mubarizahmed/desk_control/eda/desk_control_b.png

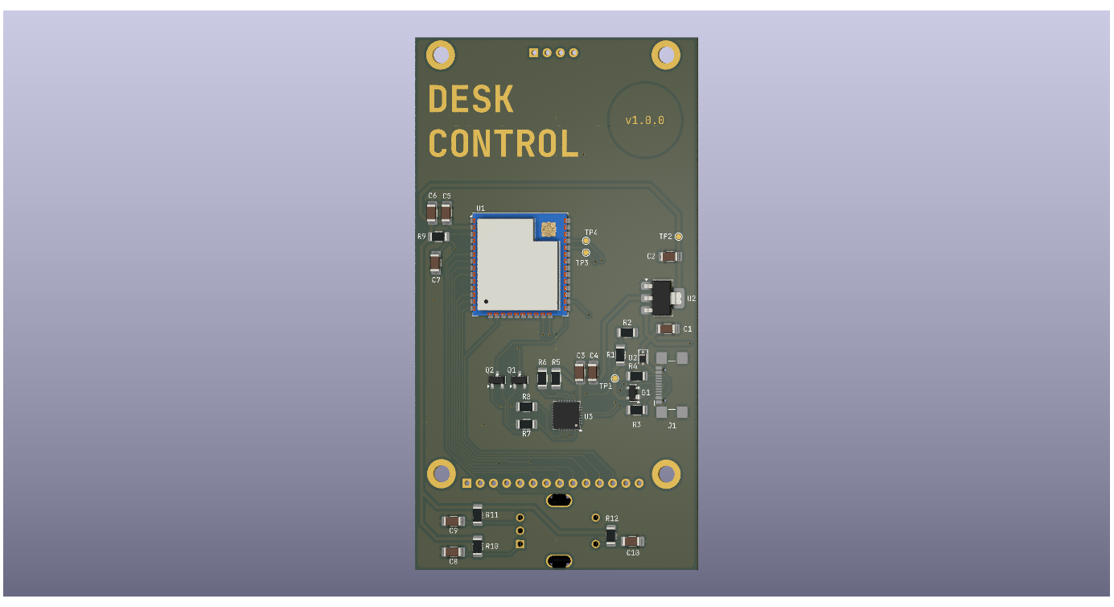
eda/desk_control_b.png
