mubarizahmed/desk_control/main/calendar_serv.h

/**
 * @file calendar_serv.h
 * @author Mubariz Ahmed (mubariz@mubariz.me)
 * @brief Header - Calendar service for fetching calendar data from a google script URL.
 * @version 0.1
 * @date 2025-04-13
 *
 */

#ifndef CALENDAR_SERV_H
#define CALENDAR_SERV_H

/* ------------------------------------------------------ */
/*                    PUBLIC FUNCTIONS                    */
/* ------------------------------------------------------ */

void calendar_task(void *pvParameters);

#endif // CALENDAR_SERV_H
