mubarizahmed/desk_control/main/time_serv.h

/**
 * @file ui.h
 * @author Mubariz Ahmed (mubariz@mubariz.me)
 * @brief Header - Time Service
 * @version 0.1
 * @date 2025-04-10
 *
 */

#ifndef TIME_SERV_H
#define TIME_SERV_H

/* ------------------------------------------------------ */
/*                    PUBLIC FUNCTIONS                    */
/* ------------------------------------------------------ */

void time_task(void *pvParameters);

#endif // TIME_SERV_H
