mubarizahmed/desk_control/main/weather_serv.h

/**
 * @file weather_serv.h
 * @author Mubariz Ahmed (mubariz@mubariz.me)
 * @brief Header - Weather service for fetching weather data from wttr.in.
 * @version 0.1
 * @date 2025-04-09
 *
 */

#ifndef WEATHER_SERV_H
#define WEATHER_SERV_H

/* ------------------------------------------------------ */
/*                    PUBLIC FUNCTIONS                    */
/* ------------------------------------------------------ */

void weather_task(void *pvParameters);

#endif // WEATHER_SERV_H
