mubarizahmed/desk_control/main/wifi_manager.h

/**
 * @file wifi_manager.c
 * @author Mubariz Ahmed (mubariz@mubariz.me)
 * @brief 	Controller for WiFi connection and event handling.
 * @version 0.1
 * @date 2025-04-09
 *
 */

#ifndef WIFI_MANAGER_H
#define WIFI_MANAGER_H

/* ------------------------------------------------------ */
/*                        INCLUDES                        */
/* ------------------------------------------------------ */

#include "esp_wifi.h"
#include "secret_conf.h"

/* ------------------------------------------------------ */
/*                      PUBLIC MACROS                     */
/* ------------------------------------------------------ */

#define ESP_WIFI_SSID CONFIG_ESP_WIFI_SSID
#define ESP_WIFI_PASS CONFIG_ESP_WIFI_PASSWORD
#define ESP_MAXIMUM_RETRY CONFIG_ESP_MAXIMUM_RETRY

#if CONFIG_ESP_WPA3_SAE_PWE_HUNT_AND_PECK
#define ESP_WIFI_SAE_MODE WPA3_SAE_PWE_HUNT_AND_PECK
#define H2E_IDENTIFIER ""
#elif CONFIG_ESP_WPA3_SAE_PWE_HASH_TO_ELEMENT
#define ESP_WIFI_SAE_MODE WPA3_SAE_PWE_HASH_TO_ELEMENT
#define H2E_IDENTIFIER CONFIG_ESP_WIFI_PW_ID
#elif CONFIG_ESP_WPA3_SAE_PWE_BOTH
#define ESP_WIFI_SAE_MODE WPA3_SAE_PWE_BOTH
#define H2E_IDENTIFIER CONFIG_ESP_WIFI_PW_ID
#endif
#if CONFIG_ESP_WIFI_AUTH_OPEN
#define ESP_WIFI_SCAN_AUTH_MODE_THRESHOLD WIFI_AUTH_OPEN
#elif CONFIG_ESP_WIFI_AUTH_WEP
#define ESP_WIFI_SCAN_AUTH_MODE_THRESHOLD WIFI_AUTH_WEP
#elif CONFIG_ESP_WIFI_AUTH_WPA_PSK
#define ESP_WIFI_SCAN_AUTH_MODE_THRESHOLD WIFI_AUTH_WPA_PSK
#elif CONFIG_ESP_WIFI_AUTH_WPA2_PSK
#define ESP_WIFI_SCAN_AUTH_MODE_THRESHOLD WIFI_AUTH_WPA2_PSK
#elif CONFIG_ESP_WIFI_AUTH_WPA_WPA2_PSK
#define ESP_WIFI_SCAN_AUTH_MODE_THRESHOLD WIFI_AUTH_WPA_WPA2_PSK
#elif CONFIG_ESP_WIFI_AUTH_WPA3_PSK
#define ESP_WIFI_SCAN_AUTH_MODE_THRESHOLD WIFI_AUTH_WPA3_PSK
#elif CONFIG_ESP_WIFI_AUTH_WPA2_WPA3_PSK
#define ESP_WIFI_SCAN_AUTH_MODE_THRESHOLD WIFI_AUTH_WPA2_WPA3_PSK
#elif CONFIG_ESP_WIFI_AUTH_WAPI_PSK
#define ESP_WIFI_SCAN_AUTH_MODE_THRESHOLD WIFI_AUTH_WAPI_PSK
#endif

/* The event group allows multiple bits for each event, but we only care about two events:
 * - we are connected to the AP with an IP
 * - we failed to connect after the maximum amount of retries */
#define WIFI_CONNECTED_BIT BIT0
#define WIFI_FAIL_BIT BIT1

#define MAX_HTTP_RECV_BUFFER 512
#define MAX_HTTP_OUTPUT_BUFFER 512

/* ------------------------------------------------------ */
/*                    PUBLIC VARIABLES                    */
/* ------------------------------------------------------ */

extern int8_t wifi_connected;
extern esp_ip4_addr_t ip_addr;

/* ------------------------------------------------------ */
/*                    PUBLIC FUNCTIONS                    */
/* ------------------------------------------------------ */

void wifi_init_sta(void);

#endif // WIFI_MANAGER_H
