mubarizahmed/desk_control/main/ui.c

/**
 * @file ui.c
 * @author Mubariz Ahmed (mubariz@mubariz.me)
 * @brief LVGL UI
 * @version 0.1
 * @date 2025-04-09
 *
 */

/* ------------------------------------------------------ */
/*                        INCLUDES                        */
/* ------------------------------------------------------ */

#include "ui.h"
#include "esp_log.h"
#include "lvgl.h"
#include "pomodoro.h"
#include "spotify_serv.h"
#include "string.h"

/* ------------------------------------------------------ */
/*                      CONFIG MACROS                     */
/* ------------------------------------------------------ */

#define UI_BLACK lv_color_hex(0x000000)
#define UI_WHITE lv_color_hex(0xFFFFFF)
#define UI_YELLOW lv_color_hex(0Xffb700)
#define UI_GREEN lv_color_hex(0X00794c)
#define UI_RED lv_color_hex(0Xed1c24)
#define UI_SPOTIFY_GREEN lv_color_hex(0X1ed760)

#define LV_LVGL_H_INCLUDE_SIMPLE

/* ------------------------------------------------------ */
/*                    PUBLIC VARIABLES                    */
/* ------------------------------------------------------ */
extern const lv_font_t jetbrains_mono_bold_8;
extern const lv_font_t jetbrains_mono_bold_10;
extern const lv_font_t jetbrains_mono_bold_12;
extern const lv_font_t jetbrains_mono_bold_14;
extern const lv_font_t jetbrains_mono_bold_18;
extern const lv_font_t jetbrains_mono_bold_50;

extern const lv_font_t jetbrains_mono_light_12;
extern const lv_font_t jetbrains_mono_light_14;
extern const lv_font_t jetbrains_mono_light_50;

extern const lv_font_t jetbrains_mono_regular_10;
extern const lv_font_t jetbrains_mono_regular_12;
extern const lv_font_t jetbrains_mono_regular_14;

extern const lv_font_t noto_color_emoji_50;
extern const lv_font_t noto_emoji_50;

/* ------------------------------------------------------ */
/*                    PRIVATE VARIABLES                   */
/* ------------------------------------------------------ */
static lv_obj_t *btn;
static lv_obj_t *scr;
static lv_obj_t *label;
static lv_display_rotation_t rotation = LV_DISP_ROTATION_0;

static lv_obj_t *time_hr_label;
static lv_obj_t *time_min_label;
static lv_obj_t *date_label;
static lv_obj_t *loc_label;

static lv_obj_t *weather_label;
static lv_obj_t *temp_label;
static lv_obj_t *loc_label;
static lv_obj_t *wind_label;

static lv_obj_t *event_1_time;
static lv_obj_t *event_1_name;
static lv_obj_t *event_2_time;
static lv_obj_t *event_2_name;

static lv_obj_t *task_1_label;
static lv_obj_t *task_2_label;
static lv_obj_t *task_3_label;
static lv_obj_t *task_4_label;

static lv_obj_t *pomodoro_overlay;
static lv_obj_t *pomodoro_overlay_label;

static lv_obj_t *sp_song_label;
static lv_obj_t *sp_artist_label;
static lv_obj_t *sp_play_icon;
static lv_obj_t *sp_cover_rect;
static lv_obj_t *sp_cover_img;
static lv_obj_t *sp_cover_img_buffer;

static lv_obj_t *circle = NULL;

static const char *TAG = "UI";

static int currentCenterX;
static int currentCenterY;

/* ------------------------------------------------------ */
/*               PRIVATE FUNCTION PROTOTYPES              */
/* ------------------------------------------------------ */
/* ---------------------- Callbacks --------------------- */

static void pomodoro_cb(lv_event_t *e);
static void pomodoro_stop_cb(lv_event_t *e);
static void spotify_play_cb(lv_event_t *e);
static void spotify_next_cb(lv_event_t *e);
static void spotify_prev_cb(lv_event_t *e);

/* --------------------- UI Elements -------------------- */

void createTimeWidget();
void createTitleWidget();
void createWeatherWidget();
void createDateWidget();
void createCalendarWidget();
void createTodoistWidget();
void createTasksWidget();
void createPomodoroWidget();
void createSpotifyWidget();

/* ----------------------- Utility ---------------------- */

void centeredGrowing(lv_obj_t *obj, int32_t size);
void lv_obj_remove_border_paddin_scrollbar(lv_obj_t *obj);
static lv_font_t *get_font_for_priority(uint8_t priority);

/* ------------------------------------------------------ */
/*                    PRIVATE FUNCTIONS                   */
/* ------------------------------------------------------ */
/* ---------------------- Callbacks --------------------- */
/**
 * @brief Pomodoro callback function. Called when the user clicks on the pomodoro button.
 *
 * @param e - lvgl event pointer
 */
static void pomodoro_cb(lv_event_t *e) {
    // get user data
    int8_t *v = (int8_t *)lv_event_get_user_data(e);
    ESP_LOGI(TAG, "Pomodoro cb %d", *v);

    startPomodoro(*v);

    // enable overlay
    lv_obj_remove_flag(pomodoro_overlay, LV_OBJ_FLAG_HIDDEN);
    lv_obj_remove_flag(pomodoro_overlay_label, LV_OBJ_FLAG_HIDDEN);

    char pomodoro_time[8];
    pomodoro_time[0] = '0' + (*v / 10); // Tens digit
    pomodoro_time[1] = '0' + (*v % 10); // Units digit
    pomodoro_time[2] = ' ';
    pomodoro_time[3] = 'm';  // Minutes
    pomodoro_time[4] = 'i';  // Minutes
    pomodoro_time[5] = 'n';  // Minutes
    pomodoro_time[6] = 's';  // Minutes
    pomodoro_time[7] = '\0'; // Null terminator

    lv_label_set_text(pomodoro_overlay_label, pomodoro_time);
}

/**
 * @brief Pomodoro stop callback function. Called when the user clicks on the pomodoro stop button.
 *
 * @param e - lvgl event pointer
 */
static void pomodoro_stop_cb(lv_event_t *e) {
    // get user data
    stopPomodoro();

    // enable overlay
    lv_obj_add_flag(pomodoro_overlay, LV_OBJ_FLAG_HIDDEN);
    lv_obj_add_flag(pomodoro_overlay_label, LV_OBJ_FLAG_HIDDEN);
    lv_obj_set_style_bg_color(pomodoro_overlay, UI_BLACK, 0);
    lv_obj_set_style_text_color(pomodoro_overlay_label, UI_WHITE, 0);
}

/**
 * @brief Spotify play/pause callback function. Called when the user clicks on the play/pause button.
 *
 * @param e - lvgl event pointer
 */
static void spotify_play_cb(lv_event_t *e) {
    // get user data
    char *play_button_val = lv_label_get_text(sp_play_icon);
    if (strcmp(play_button_val, "▶") == 0) {
        ESP_LOGI(TAG, "Spotify play cb play");
        // resume_track();
        xEventGroupSetBits(spotify_event_group, SPOTIFY_CMD_RESUME);
    } else {
        ESP_LOGI(TAG, "Spotify play cb pause");
        // pause_track();
        xEventGroupSetBits(spotify_event_group, SPOTIFY_CMD_PAUSE);
    }
}

/**
 * @brief Spotify next track callback function. Called when the user clicks on the next track button.
 *
 * @param e - lvgl event pointer
 */
static void spotify_next_cb(lv_event_t *e) {
    ESP_LOGI(TAG, "Spotify next cb");
    // next_track();
    xEventGroupSetBits(spotify_event_group, SPOTIFY_CMD_NEXT);
}

/**
 * @brief Spotify previous track callback function. Called when the user clicks on the previous track button.
 *
 * @param e - lvgl event pointer
 */
static void spotify_prev_cb(lv_event_t *e) {
    ESP_LOGI(TAG, "Spotify prev cb");
    // previous_track();
    xEventGroupSetBits(spotify_event_group, SPOTIFY_CMD_PREV);
}

/* --------------------- UI Elements -------------------- */

/**
 * @brief Create a time widget on the screen.
 *
 */
void createTimeWidget() {
    // create a rectangle for the time
    lv_obj_t *t_rect1 = lv_obj_create(scr);
    lv_obj_set_size(t_rect1, 84, 108);
    // lv_obj_align(t_rect1, LV_ALIGN_CENTER, 0, 0);
    lv_obj_set_pos(t_rect1, 6, 6);
    lv_obj_set_style_bg_color(t_rect1, UI_YELLOW, 0);
    lv_obj_remove_border_paddin_scrollbar(t_rect1);
    lv_obj_set_style_border_width(t_rect1, 2, 0);
    lv_obj_set_style_border_side(t_rect1, LV_BORDER_SIDE_FULL, 0);

    // disable scrollbar
    lv_obj_set_scrollbar_mode(t_rect1, LV_SCROLLBAR_MODE_OFF);

    time_hr_label = lv_label_create(t_rect1);
    lv_label_set_text(time_hr_label, "10");
    lv_obj_set_style_text_font(time_hr_label, &jetbrains_mono_bold_50, 0);
    lv_obj_set_style_text_color(time_hr_label, UI_BLACK, 0);
    lv_obj_set_style_text_align(time_hr_label, LV_TEXT_ALIGN_CENTER, 0);
    lv_obj_center(time_hr_label);
    lv_obj_set_style_text_letter_space(time_hr_label, -5, 0);
    lv_obj_set_pos(time_hr_label, 0, -22);

    time_min_label = lv_label_create(t_rect1);
    lv_label_set_text(time_min_label, "24");
    lv_obj_set_style_text_font(time_min_label, &jetbrains_mono_light_50, 0);
    lv_obj_set_style_text_color(time_min_label, UI_BLACK, 0);
    lv_obj_set_style_text_align(time_min_label, LV_TEXT_ALIGN_CENTER, 0);
    lv_obj_align_to(time_min_label, time_hr_label, LV_ALIGN_OUT_BOTTOM_MID, 0, -20);
    lv_obj_set_style_text_letter_space(time_min_label, -3, 0);
}

/**
 * @brief Create a title widget on the screen.
 *
 */
void createTitleWidget() {
    // create a rectangle for the time
    lv_obj_t *rect = lv_obj_create(scr);
    lv_obj_set_size(rect, 144, 20);
    // lv_obj_align(t_rect1, LV_ALIGN_CENTER, 0, 0);
    lv_obj_set_pos(rect, 90, 6);
    lv_obj_set_style_bg_color(rect, UI_BLACK, 0);
    lv_obj_remove_border_paddin_scrollbar(rect);

    // disable scrollbar
    lv_obj_set_scrollbar_mode(rect, LV_SCROLLBAR_MODE_OFF);

    lv_obj_t *title_label = lv_label_create(rect);
    lv_label_set_text(title_label, "DESK_CONTROL");
    lv_obj_set_style_text_font(title_label, &jetbrains_mono_bold_12, 0);
    lv_obj_set_style_text_color(title_label, UI_WHITE, 0);
    lv_obj_set_style_text_align(title_label, LV_TEXT_ALIGN_RIGHT, 0);
    lv_obj_align(title_label, LV_ALIGN_RIGHT_MID, -4, 0);
}

/**
 * @brief Create a weather widget on the screen.
 *
 */
void createWeatherWidget() {
    // create a rectangle for the weather
    lv_obj_t *rect = lv_obj_create(scr);
    lv_obj_set_size(rect, 146, 88);
    // lv_obj_align(t_rect1, LV_ALIGN_CENTER, 0, 0);
    lv_obj_set_pos(rect, 88, 26);
    lv_obj_set_style_bg_color(rect, UI_WHITE, 0);
    lv_obj_remove_border_paddin_scrollbar(rect);
    lv_obj_set_style_border_width(rect, 2, 0);
    lv_obj_set_style_border_side(rect, LV_BORDER_SIDE_FULL, 0);

    // Location
    lv_obj_t *loc_rect = lv_obj_create(rect);
    lv_obj_set_size(loc_rect, 60, 18);
    lv_obj_set_style_bg_color(loc_rect, UI_GREEN, 0);
    lv_obj_remove_border_paddin_scrollbar(loc_rect);
    lv_obj_set_style_border_width(loc_rect, 2, 0);
    lv_obj_set_style_border_side(loc_rect, LV_BORDER_SIDE_FULL, 0);
    lv_obj_align_to(loc_rect, rect, LV_ALIGN_BOTTOM_LEFT, 2, -2);

    loc_label = lv_label_create(loc_rect);
    lv_label_set_text(loc_label, "BOCHUM");
    lv_obj_set_style_text_font(loc_label, &jetbrains_mono_bold_12, 0);
    lv_obj_set_style_text_color(loc_label, UI_WHITE, 0);
    lv_obj_set_style_text_align(loc_label, LV_TEXT_ALIGN_CENTER, 0);
    lv_obj_center(loc_label);

    // Temp label
    temp_label = lv_label_create(rect);
    lv_label_set_text(temp_label, "25");
    lv_obj_set_style_text_font(temp_label, &jetbrains_mono_bold_50, 0);
    lv_obj_set_style_text_color(temp_label, UI_BLACK, 0);
    lv_obj_set_style_text_align(temp_label, LV_TEXT_ALIGN_RIGHT, 0);
    lv_obj_align_to(temp_label, rect, LV_ALIGN_TOP_LEFT, 5, 0);
    lv_obj_set_style_text_letter_space(temp_label, -5, 0);

    lv_obj_t *temp_unit_label = lv_label_create(rect);
    lv_label_set_text(temp_unit_label, "°C");
    lv_obj_set_style_text_font(temp_unit_label, &jetbrains_mono_bold_12, 0);
    lv_obj_set_style_text_color(temp_unit_label, UI_BLACK, 0);
    lv_obj_set_style_text_align(temp_unit_label, LV_TEXT_ALIGN_LEFT, 0);
    lv_obj_align_to(temp_unit_label, rect, LV_ALIGN_TOP_LEFT, 55, 2);

    // Wind label
    wind_label = lv_label_create(rect);
    lv_label_set_text(wind_label, "↘12km/h");
    lv_obj_set_style_text_font(wind_label, &jetbrains_mono_light_12, 0);
    lv_obj_set_style_text_color(wind_label, UI_BLACK, 0);
    lv_obj_set_style_text_align(wind_label, LV_TEXT_ALIGN_CENTER, 0);
    lv_obj_align_to(wind_label, rect, LV_ALIGN_BOTTOM_RIGHT, -13, -3);

    // Weather label
    weather_label = lv_label_create(rect);
    // lv_label_set_text(weather_label, "☀️");
    lv_label_set_text(weather_label, "☀️");
    lv_obj_set_style_text_font(weather_label, &noto_emoji_50, 0);
    lv_obj_set_style_text_color(weather_label, UI_BLACK, 0);
    lv_obj_set_style_text_align(weather_label, LV_TEXT_ALIGN_CENTER, 0);
    lv_obj_align_to(weather_label, rect, LV_ALIGN_TOP_RIGHT, -8, 10);
}

/**
 * @brief Create a date widget on the screen.
 *
 */
void createDateWidget() {
    // create a rectangle for the date
    lv_obj_t *rect = lv_obj_create(scr);
    lv_obj_set_size(rect, 84, 16);
    // lv_obj_align(t_rect1, LV_ALIGN_CENTER, 0, 0);
    lv_obj_set_pos(rect, 6, 114);
    lv_obj_set_style_bg_color(rect, UI_BLACK, 0);
    lv_obj_remove_border_paddin_scrollbar(rect);

    // Date label
    date_label = lv_label_create(rect);
    lv_label_set_text(date_label, "❱ WED 10.04.2025");
    lv_obj_set_style_text_font(date_label, &jetbrains_mono_bold_8, 0);
    lv_obj_set_style_text_color(date_label, UI_WHITE, 0);
    lv_obj_set_style_text_align(date_label, LV_TEXT_ALIGN_CENTER, 0);
    lv_obj_align_to(date_label, rect, LV_ALIGN_CENTER, 0, 0);
    // lv_obj_center(date_label);
}

/**
 * @brief Create a calendar widget on the screen.
 *
 */
void createCalendarWidget() {
    lv_obj_t *rect = lv_obj_create(scr);
    lv_obj_set_size(rect, 84, 78);
    lv_obj_set_pos(rect, 6, 128);
    lv_obj_set_style_bg_color(rect, UI_WHITE, 0);
    lv_obj_remove_border_paddin_scrollbar(rect);
    lv_obj_set_style_border_width(rect, 2, 0);
    lv_obj_set_style_border_side(rect, LV_BORDER_SIDE_FULL, 0);

    event_1_time = lv_label_create(rect);
    lv_label_set_text(event_1_time, "13:00 ↘");
    lv_obj_set_style_text_font(event_1_time, &jetbrains_mono_regular_10, 0);
    lv_obj_set_style_text_color(event_1_time, UI_BLACK, 0);
    lv_obj_set_style_text_align(event_1_time, LV_TEXT_ALIGN_LEFT, 0);
    lv_obj_align_to(event_1_time, rect, LV_ALIGN_TOP_LEFT, 5, 5);

    event_1_name = lv_label_create(rect);
    lv_label_set_text(event_1_name, "Jour Fixe");
    lv_obj_set_style_text_font(event_1_name, &jetbrains_mono_bold_10, 0);
    lv_obj_set_style_text_color(event_1_name, UI_BLACK, 0);
    lv_obj_set_style_text_align(event_1_name, LV_TEXT_ALIGN_LEFT, 0);
    lv_obj_align_to(event_1_name, rect, LV_ALIGN_TOP_LEFT, 5, 20);

    event_2_time = lv_label_create(rect);
    lv_label_set_text(event_2_time, "15:15 ↘");
    lv_obj_set_style_text_font(event_2_time, &jetbrains_mono_regular_10, 0);
    lv_obj_set_style_text_color(event_2_time, UI_BLACK, 0);
    lv_obj_set_style_text_align(event_2_time, LV_TEXT_ALIGN_LEFT, 0);
    lv_obj_align_to(event_2_time, rect, LV_ALIGN_TOP_LEFT, 5, 40);

    event_2_name = lv_label_create(rect);
    lv_label_set_text(event_2_name, "BLE Mesh W..");
    lv_obj_set_style_text_font(event_2_name, &jetbrains_mono_bold_10, 0);
    lv_obj_set_style_text_color(event_2_name, UI_BLACK, 0);
    lv_obj_set_style_text_align(event_2_name, LV_TEXT_ALIGN_LEFT, 0);
    lv_obj_align_to(event_2_name, rect, LV_ALIGN_TOP_LEFT, 5, 55);
}

/**
 * @brief Create a Spotify widget on the screen.
 *
 */
void createTasksWidget() {
    // create a rectangle for the tasks
    lv_obj_t *rect = lv_obj_create(scr);
    lv_obj_set_size(rect, 146, 94);
    lv_obj_set_pos(rect, 88, 112);
    lv_obj_set_style_bg_color(rect, UI_WHITE, 0);
    lv_obj_remove_border_paddin_scrollbar(rect);
    lv_obj_set_style_border_width(rect, 2, 0);
    lv_obj_set_style_border_side(rect, LV_BORDER_SIDE_FULL, 0);

    lv_obj_t *title_label = lv_label_create(rect);
    lv_label_set_text(title_label, "◩ TODOIST");
    lv_obj_set_style_text_font(title_label, &jetbrains_mono_bold_10, 0);
    lv_obj_set_style_text_color(title_label, UI_RED, 0);
    lv_obj_set_style_text_align(title_label, LV_TEXT_ALIGN_LEFT, 0);
    lv_obj_align_to(title_label, rect, LV_ALIGN_TOP_LEFT, 7, 3);

    task_1_label = lv_label_create(rect);
    lv_label_set_text(task_1_label, "◌ Design UI");
    lv_obj_set_style_text_font(task_1_label, &jetbrains_mono_regular_12, 0);
    lv_obj_set_style_text_color(task_1_label, UI_BLACK, 0);
    lv_obj_set_style_text_align(task_1_label, LV_TEXT_ALIGN_LEFT, 0);
    lv_obj_align_to(task_1_label, rect, LV_ALIGN_TOP_LEFT, 5, 18);

    task_2_label = lv_label_create(rect);
    lv_label_set_text(task_2_label, "◌ Implement UI");
    lv_obj_set_style_text_font(task_2_label, &jetbrains_mono_regular_12, 0);
    lv_obj_set_style_text_color(task_2_label, UI_BLACK, 0);
    lv_obj_set_style_text_align(task_2_label, LV_TEXT_ALIGN_LEFT, 0);
    lv_obj_align_to(task_2_label, rect, LV_ALIGN_TOP_LEFT, 5, 36);

    task_3_label = lv_label_create(rect);
    lv_label_set_text(task_3_label, "◌ SNTP Time");
    lv_obj_set_style_text_font(task_3_label, &jetbrains_mono_regular_12, 0);
    lv_obj_set_style_text_color(task_3_label, UI_BLACK, 0);
    lv_obj_set_style_text_align(task_3_label, LV_TEXT_ALIGN_LEFT, 0);
    lv_obj_align_to(task_3_label, rect, LV_ALIGN_TOP_LEFT, 5, 54);

    task_4_label = lv_label_create(rect);
    lv_label_set_text(task_4_label, "◌ Buy groceries");
    lv_obj_set_style_text_font(task_4_label, &jetbrains_mono_regular_12, 0);
    lv_obj_set_style_text_color(task_4_label, UI_BLACK, 0);
    lv_obj_set_style_text_align(task_4_label, LV_TEXT_ALIGN_LEFT, 0);
    lv_obj_align_to(task_4_label, rect, LV_ALIGN_TOP_LEFT, 5, 72);
}

/**
 * @brief Create a Pomodoro widget on the screen.
 *
 */
void createPomodoroWidget() {
    // create a rectangle for the tasks
    lv_obj_t *rect = lv_obj_create(scr);
    lv_obj_set_size(rect, 228, 50);
    lv_obj_set_pos(rect, 6, 206);
    lv_obj_set_style_bg_color(rect, UI_BLACK, 0);
    lv_obj_remove_border_paddin_scrollbar(rect);

    lv_obj_t *title_label_1 = lv_label_create(rect);
    lv_label_set_text(title_label_1, "POM");
    lv_obj_set_style_text_font(title_label_1, &jetbrains_mono_regular_14, 0);
    lv_obj_set_style_text_color(title_label_1, UI_RED, 0);
    lv_obj_set_style_text_align(title_label_1, LV_TEXT_ALIGN_LEFT, 0);
    lv_obj_align_to(title_label_1, rect, LV_ALIGN_TOP_LEFT, 5, 2);

    lv_obj_t *title_label_2 = lv_label_create(rect);
    lv_label_set_text(title_label_2, "ODO");
    lv_obj_set_style_text_font(title_label_2, &jetbrains_mono_regular_14, 0);
    lv_obj_set_style_text_color(title_label_2, UI_RED, 0);
    lv_obj_set_style_text_align(title_label_2, LV_TEXT_ALIGN_LEFT, 0);
    lv_obj_align_to(title_label_2, rect, LV_ALIGN_TOP_LEFT, 5, 17);

    lv_obj_t *title_label_3 = lv_label_create(rect);
    lv_label_set_text(title_label_3, "RO◎");
    lv_obj_set_style_text_font(title_label_3, &jetbrains_mono_regular_14, 0);
    lv_obj_set_style_text_color(title_label_3, UI_RED, 0);
    lv_obj_set_style_text_align(title_label_3, LV_TEXT_ALIGN_LEFT, 0);
    lv_obj_align_to(title_label_3, rect, LV_ALIGN_TOP_LEFT, 5, 32);

    lv_obj_t *p1_rect = lv_obj_create(rect);
    lv_obj_set_size(p1_rect, 34, 34);
    lv_obj_set_style_bg_color(p1_rect, UI_WHITE, 0);
    lv_obj_remove_border_paddin_scrollbar(p1_rect);
    lv_obj_align_to(p1_rect, rect, LV_ALIGN_TOP_LEFT, 48, 8);
    lv_obj_add_flag(p1_rect, LV_OBJ_FLAG_CLICKABLE);
    int8_t *p1_time = malloc(sizeof(int8_t));
    *p1_time = 2;
    lv_obj_add_event_cb(p1_rect, pomodoro_cb, LV_EVENT_CLICKED, p1_time);

    lv_obj_t *p1_label = lv_label_create(p1_rect);
    lv_label_set_text(p1_label, "30\nmin");
    lv_obj_set_style_text_font(p1_label, &jetbrains_mono_light_14, 0);
    lv_obj_set_style_text_color(p1_label, UI_BLACK, 0);
    lv_obj_set_style_text_line_space(p1_label, -3, 0);
    lv_obj_set_style_text_align(p1_label, LV_TEXT_ALIGN_CENTER, 0);
    lv_obj_center(p1_label);

    lv_obj_t *p2_rect = lv_obj_create(rect);
    lv_obj_set_size(p2_rect, 34, 34);
    lv_obj_set_style_bg_color(p2_rect, UI_WHITE, 0);
    lv_obj_remove_border_paddin_scrollbar(p2_rect);
    lv_obj_align_to(p2_rect, rect, LV_ALIGN_TOP_LEFT, 94, 8);
    lv_obj_add_flag(p2_rect, LV_OBJ_FLAG_CLICKABLE);
    int8_t *p2_time = malloc(sizeof(int8_t));
    *p2_time = 45;
    lv_obj_add_event_cb(p2_rect, pomodoro_cb, LV_EVENT_CLICKED, p2_time);

    lv_obj_t *p2_label = lv_label_create(p2_rect);
    lv_label_set_text(p2_label, "45\nmin");
    lv_obj_set_style_text_font(p2_label, &jetbrains_mono_light_14, 0);
    lv_obj_set_style_text_color(p2_label, UI_BLACK, 0);
    lv_obj_set_style_text_line_space(p2_label, -3, 0);
    lv_obj_set_style_text_align(p2_label, LV_TEXT_ALIGN_CENTER, 0);
    lv_obj_center(p2_label);

    lv_obj_t *p3_rect = lv_obj_create(rect);
    lv_obj_set_size(p3_rect, 34, 34);
    lv_obj_set_style_bg_color(p3_rect, UI_WHITE, 0);
    lv_obj_set_style_radius(p3_rect, 0, LV_PART_MAIN);
    lv_obj_remove_border_paddin_scrollbar(p3_rect);
    lv_obj_align_to(p3_rect, rect, LV_ALIGN_TOP_LEFT, 140, 8);
    lv_obj_add_flag(p3_rect, LV_OBJ_FLAG_CLICKABLE);
    int8_t *p3_time = malloc(sizeof(int8_t));
    *p3_time = 60;
    lv_obj_add_event_cb(p3_rect, pomodoro_cb, LV_EVENT_CLICKED, p3_time);

    lv_obj_t *p3_label = lv_label_create(p3_rect);
    lv_label_set_text(p3_label, "1\nHR");
    lv_obj_set_style_text_font(p3_label, &jetbrains_mono_light_14, 0);
    lv_obj_set_style_text_line_space(p3_label, -3, 0);
    lv_obj_set_style_text_color(p3_label, UI_BLACK, 0);
    lv_obj_set_style_text_align(p3_label, LV_TEXT_ALIGN_CENTER, 0);
    lv_obj_center(p3_label);

    lv_obj_t *p4_rect = lv_obj_create(rect);
    lv_obj_set_size(p4_rect, 34, 34);
    lv_obj_set_style_bg_color(p4_rect, UI_WHITE, 0);
    lv_obj_remove_border_paddin_scrollbar(p4_rect);
    lv_obj_align_to(p4_rect, rect, LV_ALIGN_TOP_LEFT, 186, 8);
    lv_obj_add_flag(p4_rect, LV_OBJ_FLAG_CLICKABLE);
    int8_t *p4_time = malloc(sizeof(int8_t));
    *p4_time = 90;
    lv_obj_add_event_cb(p4_rect, pomodoro_cb, LV_EVENT_CLICKED, p4_time);

    lv_obj_t *p4_label = lv_label_create(p4_rect);
    lv_label_set_text(p4_label, "1.5\nHR");
    lv_obj_set_style_text_font(p4_label, &jetbrains_mono_light_14, 0);
    lv_obj_set_style_text_line_space(p4_label, -3, 0);
    lv_obj_set_style_text_color(p4_label, UI_BLACK, 0);
    lv_obj_set_style_text_align(p4_label, LV_TEXT_ALIGN_CENTER, 0);
    lv_obj_center(p4_label);

    pomodoro_overlay = lv_obj_create(rect);
    lv_obj_set_size(pomodoro_overlay, 182, 50);
    lv_obj_set_style_bg_color(pomodoro_overlay, UI_BLACK, 0);
    lv_obj_remove_border_paddin_scrollbar(pomodoro_overlay);
    lv_obj_align_to(pomodoro_overlay, rect, LV_ALIGN_TOP_LEFT, 44, 0);
    lv_obj_add_flag(pomodoro_overlay, LV_OBJ_FLAG_HIDDEN);
    lv_obj_add_event_cb(pomodoro_overlay, pomodoro_stop_cb, LV_EVENT_CLICKED, NULL);

    pomodoro_overlay_label = lv_label_create(pomodoro_overlay);
    lv_label_set_text(pomodoro_overlay_label, "TIME'S UP!");
    lv_obj_set_style_text_font(pomodoro_overlay_label, &jetbrains_mono_bold_18, 0);
    lv_obj_set_style_text_color(pomodoro_overlay_label, UI_RED, 0);
    lv_obj_set_style_text_align(pomodoro_overlay_label, LV_TEXT_ALIGN_CENTER, 0);
    lv_obj_center(pomodoro_overlay_label);
    lv_obj_add_flag(pomodoro_overlay_label, LV_OBJ_FLAG_HIDDEN);
}

/**
 * @brief Create a Spotify widget on the screen.
 *
 */
void createSpotifyWidget() {
    // create a rectangle for the tasks
    lv_obj_t *rect = lv_obj_create(scr);
    lv_obj_set_size(rect, 240, 64);
    lv_obj_set_pos(rect, 0, 256);
    lv_obj_set_style_bg_color(rect, UI_SPOTIFY_GREEN, 0);
    lv_obj_remove_border_paddin_scrollbar(rect);
    lv_obj_set_style_border_width(rect, 2, 0);
    lv_obj_set_style_border_side(rect, LV_BORDER_SIDE_TOP, 0);

    sp_cover_rect = lv_obj_create(rect);
    lv_obj_set_size(sp_cover_rect, 84, 64);
    lv_obj_set_style_bg_color(sp_cover_rect, UI_BLACK, 0);
    lv_obj_remove_border_paddin_scrollbar(sp_cover_rect);
    lv_obj_align_to(sp_cover_rect, rect, LV_ALIGN_TOP_LEFT, 6, 0);

    sp_cover_img = lv_img_create(sp_cover_rect);
    // lv_img_set_src(sp_cover_img, sp_img_dsc);
    lv_obj_set_style_bg_color(rect, UI_SPOTIFY_GREEN, 0);
    lv_img_set_src(sp_cover_img, LV_SYMBOL_DUMMY "");
    lv_obj_set_style_img_recolor(sp_cover_img, UI_WHITE, 0);
    lv_obj_set_size(sp_cover_img, 64, 64);
    lv_obj_remove_border_paddin_scrollbar(sp_cover_img);
    lv_obj_align_to(sp_cover_img, sp_cover_rect, LV_ALIGN_CENTER, 0, 0);

    sp_song_label = lv_label_create(rect);
    lv_label_set_text(sp_song_label, "Now Playing");
    lv_obj_set_style_text_font(sp_song_label, &jetbrains_mono_bold_14, 0);
    lv_obj_set_style_text_color(sp_song_label, UI_BLACK, 0);
    lv_obj_set_style_text_align(sp_song_label, LV_TEXT_ALIGN_LEFT, 0);
    lv_obj_align_to(sp_song_label, rect, LV_ALIGN_TOP_LEFT, 100, 2);

    sp_artist_label = lv_label_create(rect);
    lv_label_set_text(sp_artist_label, "Artist");
    lv_obj_set_style_text_font(sp_artist_label, &jetbrains_mono_light_12, 0);
    lv_obj_set_style_text_color(sp_artist_label, UI_BLACK, 0);
    lv_obj_set_style_text_align(sp_artist_label, LV_TEXT_ALIGN_LEFT, 0);
    lv_obj_align_to(sp_artist_label, rect, LV_ALIGN_TOP_LEFT, 100, 18);

    // create a rectangle for the prev, play/pause, next button
    lv_obj_t *sp_prev_btn = lv_obj_create(rect);
    lv_obj_set_size(sp_prev_btn, 32, 22);
    lv_obj_set_style_bg_color(sp_prev_btn, UI_BLACK, 0);
    lv_obj_remove_border_paddin_scrollbar(sp_prev_btn);
    lv_obj_align_to(sp_prev_btn, rect, LV_ALIGN_TOP_LEFT, 100, 38);
    lv_obj_add_flag(sp_prev_btn, LV_OBJ_FLAG_CLICKABLE);
    lv_obj_add_event_cb(sp_prev_btn, spotify_prev_cb, LV_EVENT_CLICKED, NULL);

    lv_obj_t *sp_prev_icon = lv_label_create(sp_prev_btn);
    lv_label_set_text(sp_prev_icon, "«");
    lv_obj_set_style_text_font(sp_prev_icon, &jetbrains_mono_bold_18, 0);
    lv_obj_set_style_text_color(sp_prev_icon, UI_WHITE, 0);
    lv_obj_set_style_text_align(sp_prev_icon, LV_TEXT_ALIGN_CENTER, 0);
    lv_obj_align_to(sp_prev_icon, sp_prev_btn, LV_ALIGN_CENTER, 0, -2);

    lv_obj_t *sp_play_btn = lv_obj_create(rect);
    lv_obj_set_size(sp_play_btn, 32, 22);
    lv_obj_set_style_bg_color(sp_play_btn, UI_BLACK, 0);
    lv_obj_remove_border_paddin_scrollbar(sp_play_btn);
    lv_obj_align_to(sp_play_btn, rect, LV_ALIGN_TOP_LEFT, 147, 38);
    lv_obj_add_flag(sp_play_btn, LV_OBJ_FLAG_CLICKABLE);
    lv_obj_add_event_cb(sp_play_btn, spotify_play_cb, LV_EVENT_CLICKED, NULL);

    sp_play_icon = lv_label_create(sp_play_btn);
    lv_label_set_text(sp_play_icon, "▶");
    lv_obj_set_style_text_font(sp_play_icon, &jetbrains_mono_bold_18, 0);
    lv_obj_set_style_text_color(sp_play_icon, UI_WHITE, 0);
    lv_obj_set_style_text_align(sp_play_icon, LV_TEXT_ALIGN_CENTER, 0);
    lv_obj_center(sp_play_icon);

    lv_obj_t *sp_next_btn = lv_obj_create(rect);
    lv_obj_set_size(sp_next_btn, 32, 22);
    lv_obj_set_style_bg_color(sp_next_btn, UI_BLACK, 0);
    lv_obj_remove_border_paddin_scrollbar(sp_next_btn);
    lv_obj_align_to(sp_next_btn, rect, LV_ALIGN_TOP_LEFT, 194, 38);
    lv_obj_add_flag(sp_next_btn, LV_OBJ_FLAG_CLICKABLE);
    lv_obj_add_event_cb(sp_next_btn, spotify_next_cb, LV_EVENT_CLICKED, NULL);

    lv_obj_t *sp_next_icon = lv_label_create(sp_next_btn);
    lv_label_set_text(sp_next_icon, "»");
    lv_obj_set_style_text_font(sp_next_icon, &jetbrains_mono_bold_18, 0);
    lv_obj_set_style_text_color(sp_next_icon, UI_WHITE, 0);
    lv_obj_set_style_text_align(sp_next_icon, LV_TEXT_ALIGN_CENTER, 0);
    lv_obj_align_to(sp_next_icon, sp_next_btn, LV_ALIGN_CENTER, 0, -2);
}

/* ----------------------- Utility ---------------------- */

/**
 * @brief Animation function to grow the circle to the specified size
 *        and center it at the current coordinates.
 *
 *
 * @param obj - pointer to the object to animate
 * @param size - size to grow to
 */
void centeredGrowing(lv_obj_t *obj, int32_t size) {
    lv_obj_set_size(obj, size, size);
    lv_obj_set_pos(obj, currentCenterX - size / 2, currentCenterY - size / 2);
}

/**
 * @brief Utility function to remove border, padding and scrollbar from an object.
 *
 */
void lv_obj_remove_border_paddin_scrollbar(lv_obj_t *obj) {
    lv_obj_set_style_radius(obj, 0, LV_PART_MAIN);
    lv_obj_set_style_border_color(obj, UI_BLACK, 0);
    lv_obj_set_style_border_width(obj, 0, 0);
    lv_obj_set_style_border_side(obj, LV_BORDER_SIDE_NONE, 0);
    lv_obj_set_scrollbar_mode(obj, LV_SCROLLBAR_MODE_OFF);
    lv_obj_set_style_pad_left(obj, 0, 0);
    lv_obj_set_style_pad_right(obj, 0, 0);
    lv_obj_set_style_pad_top(obj, 0, 0);
    lv_obj_set_style_pad_bottom(obj, 0, 0);
}

/**
 * @brief Utility function to set the font for a label based on the priority.
 *
 * @param label The label to set the font for.
 * @param priority The priority of the label (0-4).
 */
static lv_font_t *get_font_for_priority(uint8_t priority) {
    switch (priority) {
    case 4:
        return &jetbrains_mono_bold_12;
    case 3:
        return &jetbrains_mono_regular_12;
    default:
        return &jetbrains_mono_light_12;
    }
}

/* ------------------------------------------------------ */
/*                    PUBLIC FUNCTINOS                    */
/* ------------------------------------------------------ */

/**
 * @brief Function to create a circle at the specified coordinates.
 *        Useful for debugging touch debugging.
 *
 *
 * @param centerX - X coordinate of the center of the circle
 * @param centerY - Y coordinate of the center of the circle
 */
void addCircle(int centerX, int centerY) {
    // delete the previous circle if it exists
    if (circle)
        lv_obj_del(circle);

    // create style
    lv_style_t *style = malloc(sizeof(lv_style_t));
    lv_style_init(style);
    lv_style_set_radius(style, 10);
    lv_style_set_bg_opa(style, LV_OPA_COVER);
    lv_style_set_bg_color(style, lv_color_hex(0));

    // create object for drawing a circle, set style, and remove clickable flag
    circle = lv_obj_create(lv_scr_act());
    lv_obj_remove_style_all(circle);
    lv_obj_add_style(circle, style, 0);
    lv_obj_clear_flag(circle, LV_OBJ_FLAG_CLICKABLE);

    // initial size is 0
    lv_obj_set_size(circle, 0, 0);
    currentCenterX = centerX;
    currentCenterY = centerY;
    lv_obj_set_pos(circle, centerX, centerY);

    // animation for increasing the size of the circle
    static lv_anim_t a;
    lv_anim_init(&a);
    lv_anim_set_var(&a, circle);
    lv_anim_set_exec_cb(&a, (lv_anim_exec_xcb_t)centeredGrowing);
    lv_anim_set_values(&a, 0, 20);
    lv_anim_set_time(&a, 300);
    a.act_time = 0;
    lv_anim_start(&a);
}

/**
 * @brief Creates the UI for the LVGL application.
 *
 * @param disp
 */
void lvgl_app_ui(lv_display_t *disp) {
    scr = lv_display_get_screen_active(disp);

    createTimeWidget();
    createTitleWidget();
    createWeatherWidget();
    createDateWidget();
    createCalendarWidget();
    createTasksWidget();
    createPomodoroWidget();
    createSpotifyWidget();
}

/**
 * @brief Set the weather data to the label.
 *
 * @param data Weather data string in the format "weather_location_temp_wind_humidity_moon_pressure"
 */
void setWeatherData(char *data) {

    ESP_LOGI(TAG, "setWeatherData data: %s", data);
    // split on _
    char *token = strtok(data, "_");
    char *temp = NULL;
    char *wind = NULL;
    char *humidity = NULL;
    char *pressure = NULL;
    char *moon = NULL;
    char *weather = NULL;
    char *location = NULL;

    int i = 0;
    while (token != NULL) {
        switch (i) {
        case 0:
            weather = token;
            break;
        case 1:
            location = token;
            break;
        case 2:
            temp = token;
            break;
        case 3:
            wind = token;
            break;
        case 4:
            humidity = token;
            break;
        case 5:
            moon = token;
            break;
        case 6:
            pressure = token;
            break;
        default:
            break;
        }
        i++;
        token = strtok(NULL, "_");
    }
    // set the text of the label to the weather data
    lv_label_set_text(weather_label, weather);

    // find length of temp string
    int len = strlen(temp);

    // remove the last 2 characters from the string
    temp[len - 2] = '\0';
    // remove first 2 characters from the string
    temp = temp + 1;

    lv_label_set_text(temp_label, temp);

    len = strlen(location);
    // capitalize the entire string
    for (int i = 0; i < len; i++) {
        if (location[i] >= 'a' && location[i] <= 'z') {
            location[i] = location[i] - 32;
        }
    }

    lv_label_set_text(loc_label, location);
    lv_label_set_text(wind_label, wind);

    // ESP_LOGI(TAG, "Weather data: %s", data);
}

/**
 * @brief Set the time and date to the label.
 *
 * @param hr Hour in 24-hour format.
 * @param min Minute.
 * @param date Date string in the format "DAY DD.MM.YYYY".
 */
void setTime(int hr, int min, char *date) {
    // check if the time labels are created
    if (time_hr_label == NULL || time_min_label == NULL) {
        ESP_LOGE(TAG, "Time labels not created yet.");
        return;
    }

    // create a string for the time data
    char hr_str[3];  // 2 digits + null terminator
    char min_str[3]; // 2 digits + null terminator

    // Convert the integers to strings
    hr_str[0] = '0' + (hr / 10); // Tens place
    hr_str[1] = '0' + (hr % 10); // Units place
    hr_str[2] = '\0';            // Null terminator

    min_str[0] = '0' + (min / 10); // Tens place
    min_str[1] = '0' + (min % 10); // Units place
    min_str[2] = '\0';             // Null terminator

    // capitalize the date string
    int len = strlen(date);
    for (int i = 0; i < len; i++) {
        if (date[i] >= 'a' && date[i] <= 'z') {
            date[i] = date[i] - 32;
        }
    }

    // set the text of the label to the time data
    lv_label_set_text(time_hr_label, hr_str);
    lv_label_set_text(time_min_label, min_str);
    lv_label_set_text(date_label, date);
}

/**
 * @brief Set the Pomodoro overlay to flash red or white.
 *
 * @param red True to flash red, false to flash white.
 */
void flashPomodoroOverlay(bool red) {

    if (red) {
        lv_obj_set_style_bg_color(pomodoro_overlay, UI_RED, 0);
        lv_obj_set_style_text_color(pomodoro_overlay_label, UI_WHITE, 0);
    } else {
        lv_obj_set_style_bg_color(pomodoro_overlay, UI_WHITE, 0);
        lv_obj_set_style_text_color(pomodoro_overlay_label, UI_BLACK, 0);
    }
}

/**
 * @brief Set the text on the Pomodoro overlay.
 *
 * @param text - remaining time in the format "00:00" or Time's up!
 */
void setPomodoro(char *text) {
    lv_label_set_text(pomodoro_overlay_label, text);
}

/**
 * @brief Set the calendar data to the widget.
 *
 * @param data Calendar data string in the format "e1_time;e1_name;e2_time;e2_name".
 */
void setCalendarData(char *data) {
    // split on ;
    char *token = strtok(data, ";");
    char *e1_time = NULL;
    char *e1_name = NULL;
    char *e2_time = NULL;
    char *e2_name = NULL;

    int i = 0;
    while (token != NULL) {
        switch (i) {
        case 0:
            e1_time = token;
            break;
        case 1:
            e1_name = token;
            break;
        case 2:
            e2_time = token;
            break;
        case 3:
            e2_name = token;
            break;
        default:
            break;
        }
        i++;
        token = strtok(NULL, ";");
    }
    lv_label_set_text(event_1_time, e1_time);
    lv_label_set_text(event_1_name, e1_name);
    lv_label_set_text(event_2_time, e2_time);
    lv_label_set_text(event_2_name, e2_name);
}

/**
 * @brief Set the Spotify data to the widget.
 *
 * @param name Name of the song.
 * @param artist Name of the artist.
 * @param playing True if playing, false if paused.
 */
void setSpotifyTextData(char *name, char *artist, bool playing) {
    lv_label_set_text(sp_song_label, name);
    lv_label_set_text(sp_artist_label, artist);
    lv_label_set_text(sp_play_icon, playing ? "■" : "▶");
}

/**
 * @brief Set the Spotify data to the widget and the cover image.
 *
 * @param name Name of the song.
 * @param artist Name of the artist.
 * @param image Image data in RGB565 format.
 * @param playing True if playing, false if paused.
 */
void setSpotifyData(char *name, char *artist, char *image, bool playing) {
    setSpotifyTextData(name, artist, playing);

    if (sp_cover_img != NULL) {
        lv_obj_del(sp_cover_img);
    }

    if (sp_cover_img_buffer != NULL) {
        free(sp_cover_img_buffer);
    }
    sp_cover_img_buffer = malloc(64 * 64 * 2);
    memcpy(sp_cover_img_buffer, image, 64 * 64 * 2);

    sp_cover_img = lv_canvas_create(sp_cover_rect);
    lv_obj_set_size(sp_cover_img, 64, 64);
    lv_obj_center(sp_cover_img);
    lv_obj_set_style_bg_color(sp_cover_img, UI_BLACK, 0);
    lv_obj_remove_border_paddin_scrollbar(sp_cover_img);
    lv_canvas_set_buffer(sp_cover_img, sp_cover_img_buffer, 64, 64, LV_COLOR_FORMAT_RGB565);
    // lv_canvas_copy_buf(canvas, image, 64, 64);
}

/**
 * @brief Set the Todoist data to the widget.
 *
 * @param data Todoist task data array.
 * @param count Number of tasks.
 */
void setTodoistData(TodoistTaskData *data, int count) {
    lv_obj_t *task_labels[] = {
        task_1_label,
        task_2_label,
        task_3_label,
        task_4_label};

    int total_slots = sizeof(task_labels) / sizeof(task_labels[0]);

    for (int i = 0; i < total_slots; i++) {
        if (i < count) {
            char task_name[25];
            snprintf(task_name, sizeof(task_name), "◌ %s", data[i].task_name);
            lv_label_set_text(task_labels[i], task_name);
            lv_obj_set_style_text_font(task_labels[i], get_font_for_priority(data[i].task_priority), 0);
        } else {
            // Clear the label if no task is assigned
            lv_label_set_text(task_labels[i], "");
        }
    }
}
